planmarks/sentinel-wallet/Sentinel-firmware-v1a/i18n.cpp

#include "i18n.h"

// Every non-ASCII character used below was verified present in the actual
// u8g2 font binary data (not assumed) before being used here - see the
// font-selection note in i18n.h. Strings are plain UTF-8 literals; every
// draw call that might render one of these uses u8g2's drawUTF8()/
// getUTF8Width() (see display.cpp), never the plain (non-UTF8) drawStr()/
// getStrWidth(), so multi-byte characters decode to the correct glyph.

namespace i18n {

namespace {

// [LANG_SUPPORTED_COUNT][S_COUNT], indexed [lang][id]. Row order matches
// Lang; column order matches StrId - keep both in sync.
const char *const kStrings[LANG_SUPPORTED_COUNT][S_COUNT] = {
  // ---- English (LANG_EN) ----
  {
    "Settings",
    "Lock Device",
    "Power Off",
    "Install Coins",
    "Battery",
    "Battery Saver",
    "Language",
    "Device Information",
    "Uninstall All Coins",
    "Change PIN",
    "Reset Device",
    "Off",
    "1 minute",
    "3 minutes",
    "5 minutes",
    "10 minutes",
    "Firmware:",
    "Enter PIN",
    "Wiped",
    "Too many tries",
    "Denied",
    "Wrong PIN",
    "tries left",
    "Error",
    "storage fault",
    "Uninstalled",
    "All coins removed",
    "Hold OK to uninstall\nall coins from the\ndevice",
    "Current PIN",
    "New PIN",
    "Confirm PIN",
    "Cancelled",
    "PIN unchanged",
    "Wrong PIN",
    "Mismatch",
    "try again",
    "PIN Changed",
    "New PIN saved",
    "Hold OK to set\na new PIN",
    "Hold OK to reset\nyour device",
    "Reset aborted",
    "Reset cancelled",
    "Reset",
    "Device erased\nRebooting...",
  },
  // ---- Spanish (LANG_ES) ----
  {
    "Ajustes",
    "Bloquear dispositivo",
    "Apagar",
    "Instalar monedas",
    "Batería",
    "Ahorro de batería",
    "Idioma",
    "Información del dispositivo",
    "Desinstalar todas las monedas",
    "Cambiar PIN",
    "Restablecer dispositivo",
    "Desactivado",
    "1 minuto",
    "3 minutos",
    "5 minutos",
    "10 minutos",
    "Firmware:",
    "Introducir PIN",
    "Borrado",
    "Demasiados intentos",
    "Denegado",
    "PIN incorrecto",
    "intentos restantes",
    "Error",
    "fallo de almacenamiento",
    "Desinstalado",
    "Todas las monedas eliminadas",
    "Mantén OK para\ndesinstalar todas las\nmonedas del dispositivo",
    "PIN actual",
    "Nuevo PIN",
    "Confirmar PIN",
    "Cancelado",
    "PIN sin cambios",
    "PIN incorrecto",
    "No coincide",
    "inténtalo de nuevo",
    "PIN cambiado",
    "Nuevo PIN guardado",
    "Mantén OK para\nestablecer un nuevo PIN",
    "Mantén OK para\nrestablecer el dispositivo",
    "Restablecimiento cancelado",
    "Restablecimiento cancelado",
    "Restablecido",
    "Dispositivo borrado\nReiniciando...",
  },
  // ---- Portuguese (LANG_PT) ----
  {
    "Definições",
    "Bloquear dispositivo",
    "Desligar",
    "Instalar moedas",
    "Bateria",
    "Poupança de bateria",
    "Idioma",
    "Informações do dispositivo",
    "Desinstalar todas as moedas",
    "Alterar PIN",
    "Redefinir dispositivo",
    "Desativado",
    "1 minuto",
    "3 minutos",
    "5 minutos",
    "10 minutos",
    "Firmware:",
    "Inserir PIN",
    "Apagado",
    "Demasiadas tentativas",
    "Negado",
    "PIN incorreto",
    "tentativas restantes",
    "Erro",
    "falha de armazenamento",
    "Desinstalado",
    "Todas as moedas removidas",
    "Mantenha OK para\ndesinstalar todas as\nmoedas do dispositivo",
    "PIN atual",
    "Novo PIN",
    "Confirmar PIN",
    "Cancelado",
    "PIN inalterado",
    "PIN incorreto",
    "Não coincide",
    "tente novamente",
    "PIN alterado",
    "Novo PIN guardado",
    "Mantenha OK para\ndefinir um novo PIN",
    "Mantenha OK para\nrepor o dispositivo",
    "Reposição cancelada",
    "Reposição cancelada",
    "Reiniciado",
    "Dispositivo apagado\nReiniciando...",
  },
  // ---- Estonian (LANG_ET) ----
  {
    "Seaded",
    "Lukusta seade",
    "Lülita välja",
    "Installi mündid",
    "Aku",
    "Aku säästmine",
    "Keel",
    "Seadme teave",
    "Eemalda kõik mündid",
    "Muuda PIN-koodi",
    "Lähtesta seade",
    "Väljas",
    "1 minut",
    "3 minutit",
    "5 minutit",
    "10 minutit",
    "Püsivara:",
    "Sisesta PIN",
    "Kustutatud",
    "Liiga palju katseid",
    "Keeldutud",
    "Vale PIN",
    "katset jäänud",
    "Viga",
    "mäluviga",
    "Eemaldatud",
    "Kõik mündid eemaldatud",
    "Hoia OK all, et\neemaldada kõik mündid\nseadmest",
    "Praegune PIN",
    "Uus PIN",
    "Kinnita PIN",
    "Tühistatud",
    "PIN muutmata",
    "Vale PIN",
    "Ei kattu",
    "proovi uuesti",
    "PIN muudetud",
    "Uus PIN salvestatud",
    "Hoia OK all, et\nmäärata uus PIN",
    "Hoia OK all, et\nlähtestada seade",
    "Lähtestamine katkestatud",
    "Lähtestamine tühistatud",
    "Lähtestatud",
    "Seade kustutatud\nTaaskäivitub...",
  },
  // ---- Russian (LANG_RU) ----
  {
    "Настройки",
    "Заблокировать",
    "Выключить",
    "Установить монеты",
    "Батарея",
    "Экономия батареи",
    "Язык",
    "Информация об устройстве",
    "Удалить все монеты",
    "Изменить PIN",
    "Сбросить устройство",
    "Выкл",
    "1 минута",
    "3 минуты",
    "5 минут",
    "10 минут",
    "Прошивка:",
    "Введите PIN",
    "Стёрто",
    "Слишком много попыток",
    "Отказано",
    "Неверный PIN",
    "попыток осталось",
    "Ошибка",
    "ошибка памяти",
    "Удалено",
    "Все монеты удалены",
    "Удерживайте OK,\nчтобы удалить все\nмонеты с устройства",
    "Текущий PIN",
    "Новый PIN",
    "Подтвердите PIN",
    "Отменено",
    "PIN не изменён",
    "Неверный PIN",
    "Не совпадает",
    "попробуйте снова",
    "PIN изменён",
    "Новый PIN сохранён",
    "Удерживайте OK,\nчтобы задать новый PIN",
    "Удерживайте OK,\nчтобы сбросить устройство",
    "Сброс отменён",
    "Сброс отменён",
    "Сброшено",
    "Устройство стёрто\nПерезагрузка...",
  },
};

}  // namespace

const char *tr(uint8_t lang, StrId id) {
  if (lang >= LANG_SUPPORTED_COUNT) lang = LANG_EN;
  if (id >= S_COUNT) return "";
  return kStrings[lang][id];
}

}  // namespace i18n
