planmarks/sentinel-wallet/Sentinel-firmware-v1a/ton.h

#pragma once
//
// TON (Toncoin) support — wallet contract v4R2 (structured so W5 can be added).
//
//   Derivation: SLIP-0010 ed25519 on m/44'/607'/0'  (Ledger-style path). NOTE:
//               this does NOT match Tonkeeper's native-mnemonic accounts — a
//               BIP39 seed fundamentally can't reproduce TON's native scheme.
//               Verify the address against a wallet/tool using this same path.
//   Address:    hash of the v4R2 StateInit cell {code, data{seqno=0, walletId,
//               pubkey, plugins=0}} -> user-friendly bounceable mainnet address
//               (base64url, "EQ...").
//   Signing:    BLIND — the host provides the 32-byte message hash to sign; the
//               device ed25519-signs it and shows the hash for verification.
//               App sends:    TON|acct|msgHashHex   (msgHash = 32 bytes)
//               Device sends: TON-SIG> <64-byte ed25519 signature hex>
//
// Address derivation (the cell-representation hashing this file implements)
// was independently verified 2026-07-31 against the `tonsdk` Python library:
// a faithful Python port of this exact algorithm (hashCell/parseBoc/address)
// produced a byte-identical address to tonsdk's own computation for a test
// keypair. The wallet v4R2 transfer message this address's private key signs
// (built app-side in lib/tx/ton_tx.dart) was verified the same way — signing
// message hash, message body hash, and final message hash all matched
// tonsdk's output exactly for a reference transfer.
//
#include <Arduino.h>

namespace ton {

// TON (EQ...) address for account `index`.
String address(const uint8_t *entropy, size_t entLen,
               const char *passphrase, uint32_t index);

// Raw 32-byte ed25519 public key (hex, no prefix) for account `index`.
// Unlike SOL/XLM/NEAR, a TON address is a hash of a StateInit cell (which
// embeds the pubkey) — not reversible — so the app needs the raw pubkey to
// build the wallet's data cell for state_init on a wallet's first ever
// outgoing transaction (which deploys the contract in the same message).
String pubKeyHex(const uint8_t *entropy, size_t entLen,
                 const char *passphrase, uint32_t index);

// Parse "TON|acct|msgHashHex" (32-byte hash). Returns true if well-formed.
bool loadTx(const String &line);

// First 8 hex chars of the message hash to be signed (on-screen verification).
String txHashHex();

// ed25519-sign the loaded hash. Returns 64-byte signature hex, "" on failure.
String signTx(const uint8_t *entropy, size_t entLen, const char *passphrase);

void clearTx();

}  // namespace ton
